abish7643/Laverna-V2.0/SensorTest/QTRRCRawValuesExample/QTRRCRawValuesExample.ino

#include <QTRSensors.h>

// This example is designed for use with eight RC QTR sensors. These
// reflectance sensors should be connected to digital pins 3 to 10. The
// sensors' emitter control pin (CTRL or LEDON) can optionally be connected to
// digital pin 2, or you can leave it disconnected and remove the call to
// setEmitterPin().
//
//Prints the sensor values to
// the serial monitor as numbers from 0 (maximum reflectance) to 2500 (minimum
// reflectance; this is the default RC timeout, which can be changed with
// setTimeout()).

QTRSensors qtr;

const uint8_t SensorCount = 8;
uint16_t sensorValues[SensorCount];

void setup()
{
  // configure the sensors
  qtr.setTypeRC();
  qtr.setSensorPins((const uint8_t[]){2, 3, 4, 5, 6, 7, 8, 9}, SensorCount);
  qtr.setEmitterPin(13);

  Serial.begin(9600);
}


void loop()
{
  // read raw sensor values
  qtr.read(sensorValues);

  // print the sensor values as numbers from 0 to 2500, where 0 means maximum
  // reflectance and 2500 means minimum reflectance
  for (uint8_t i = 0; i < SensorCount; i++)
  {
    Serial.print(sensorValues[i]);
    Serial.print('\t');
  }
  Serial.println();

  delay(250);
}
